Ausdauersportler/IMAC-EFI-BOOT-SCREEN/images/0201jumpers.jpg

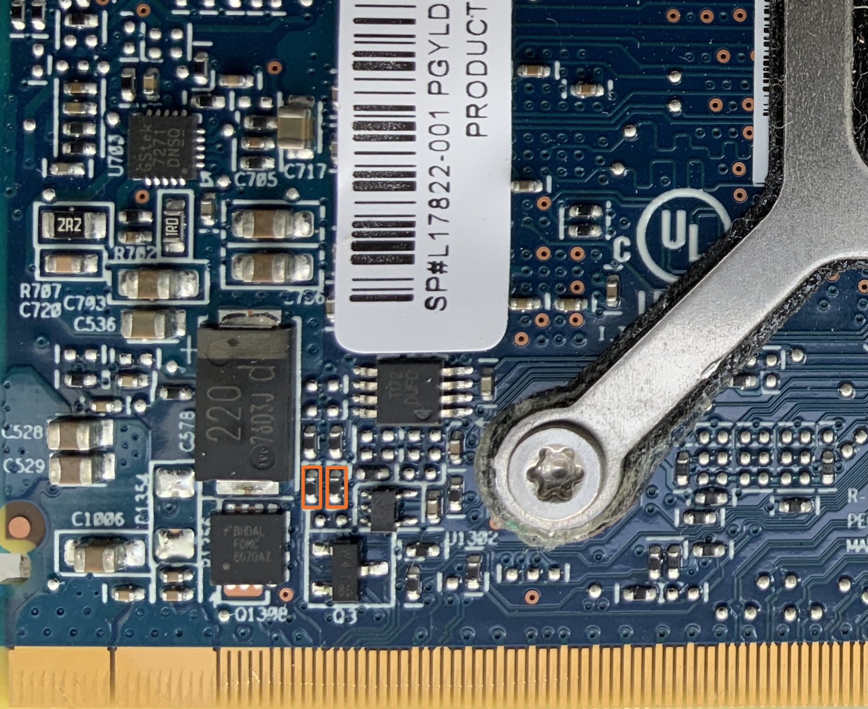
images/0201jumpers.jpg
