Ausdauersportler/IMAC-EFI-BOOT-SCREEN/images/0201jumpers_removed.jpg

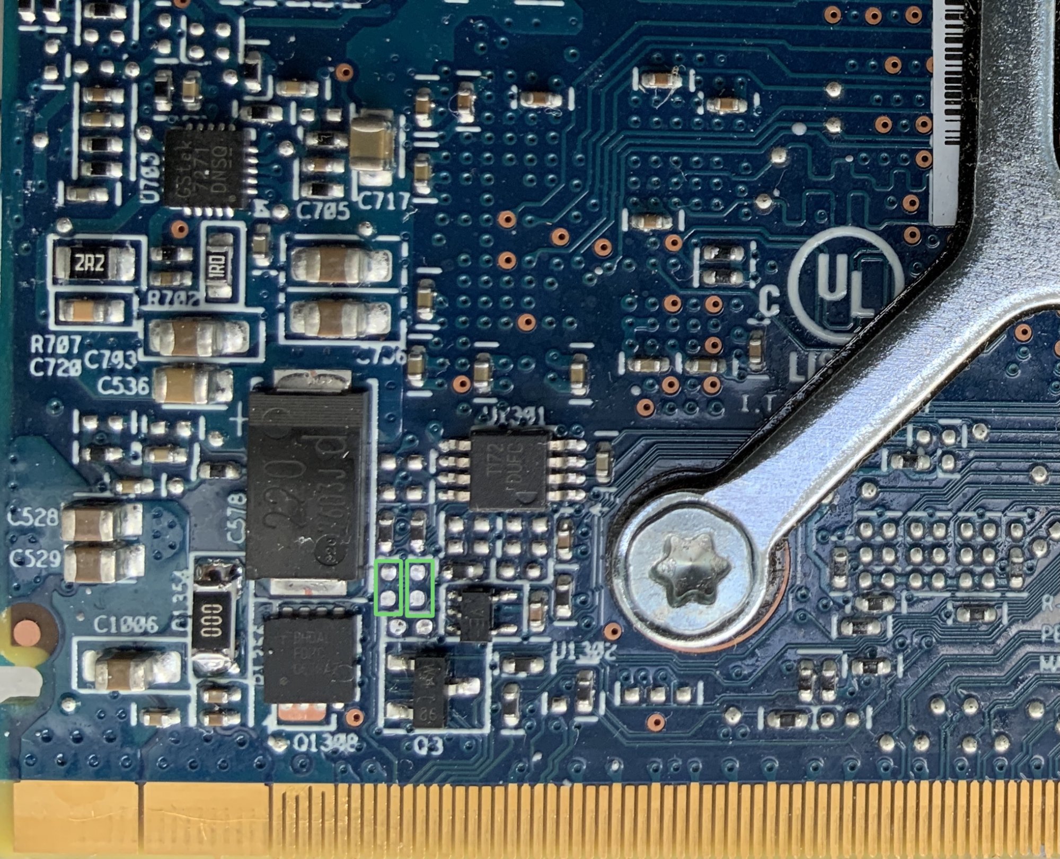
images/0201jumpers_removed.jpg
