Ausdauersportler/IMAC-EFI-BOOT-SCREEN/images/add-onPCB_conn.png

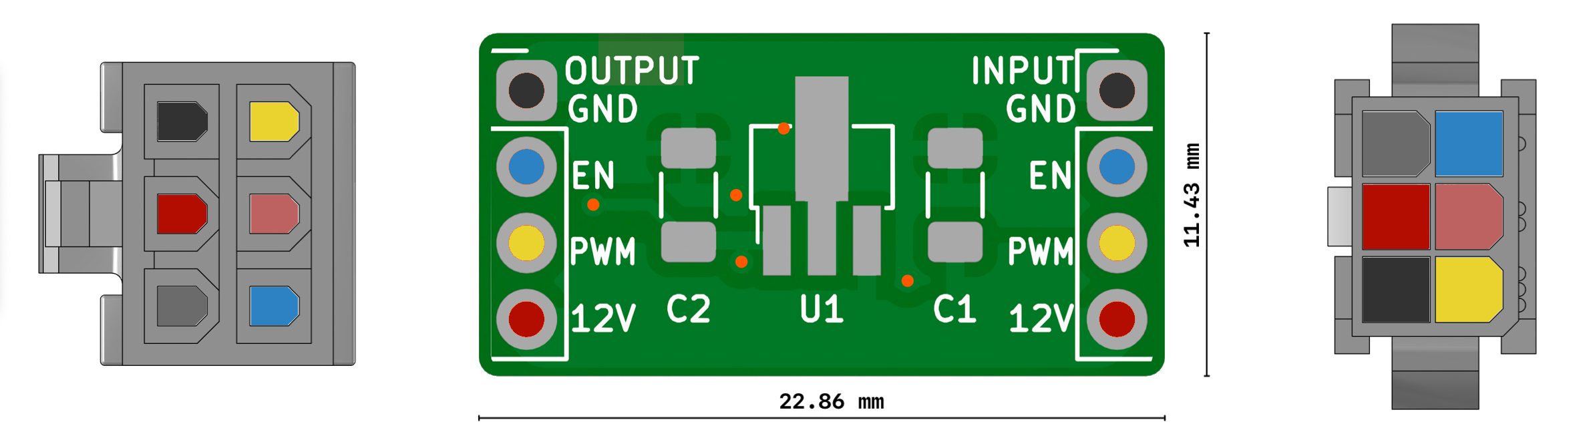
images/add-onPCB_conn.png
