Ausdauersportler/IMAC-EFI-BOOT-SCREEN/images/bottom_moddedWX4170.jpg

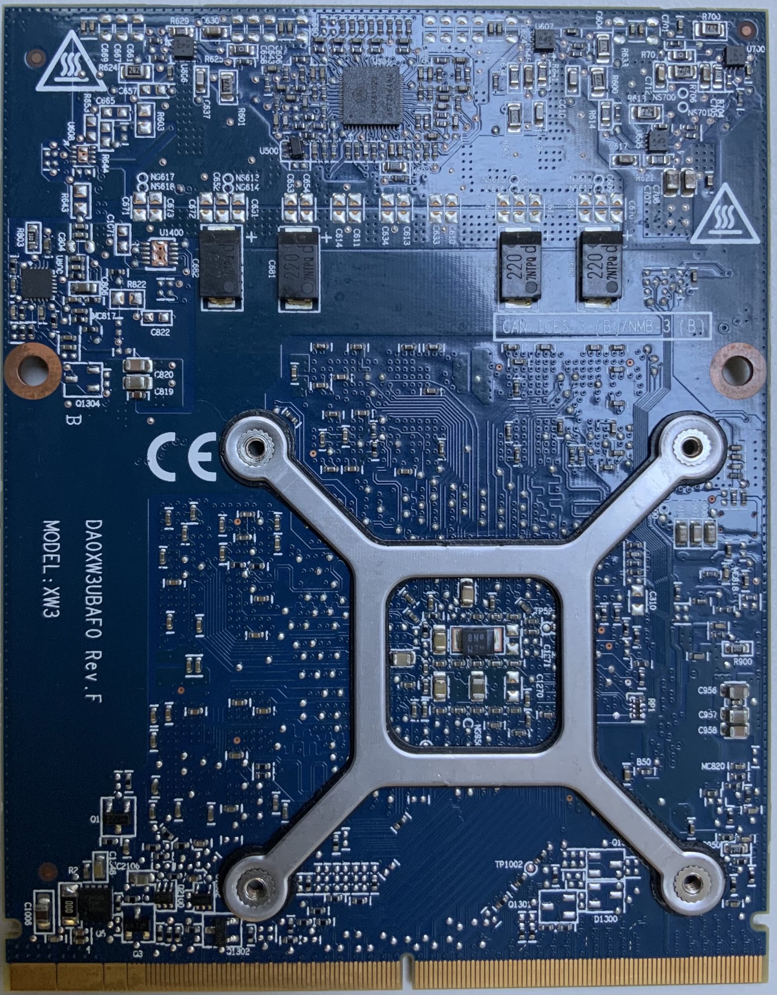
images/bottom_moddedWX4170.jpg
