Ausdauersportler/IMAC-EFI-BOOT-SCREEN/images/bottom_origWX4170.jpg

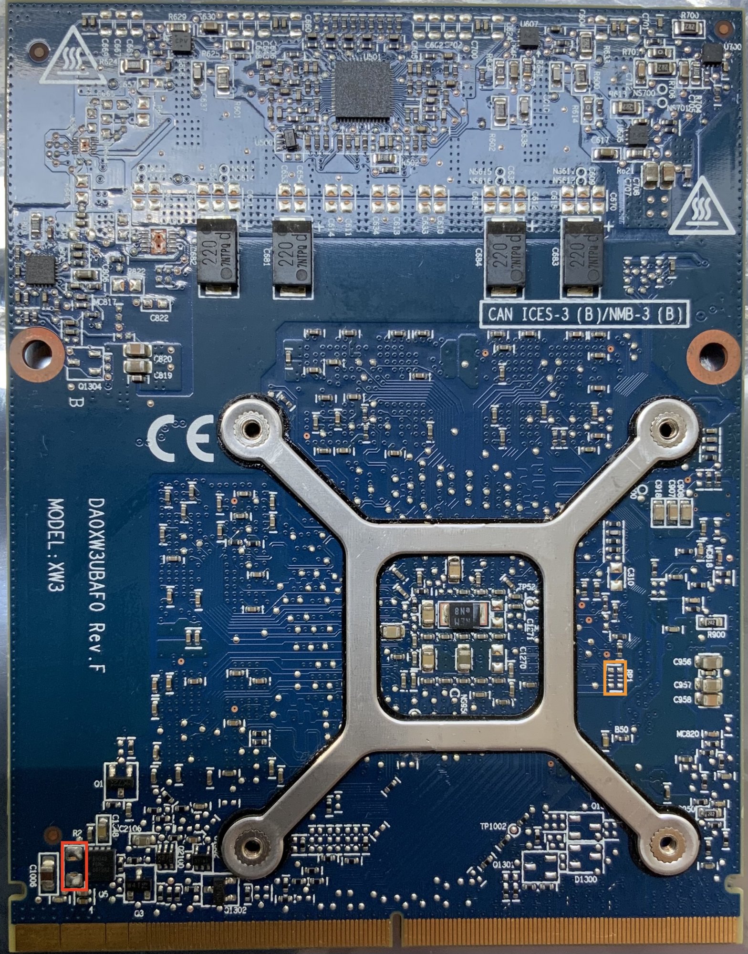
images/bottom_origWX4170.jpg
