Ausdauersportler/IMAC-EFI-BOOT-SCREEN/images/EFI-TABLES.png

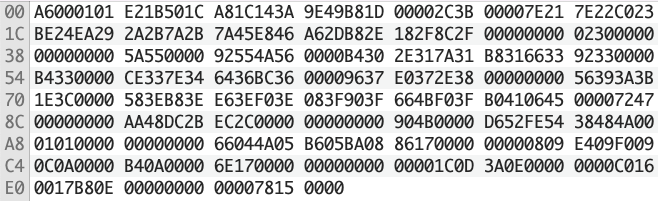
images/EFI-TABLES.png
