Ausdauersportler/IMAC-EFI-BOOT-SCREEN/images/GOP-TABLES.png

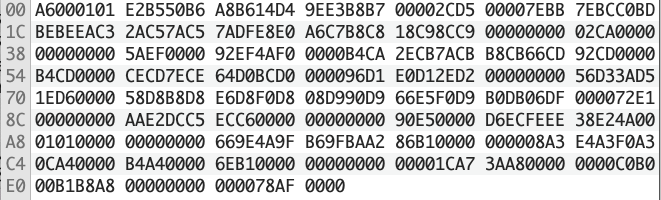
images/GOP-TABLES.png
