Ausdauersportler/IMAC-EFI-BOOT-SCREEN/images/GRML-FLASH.png

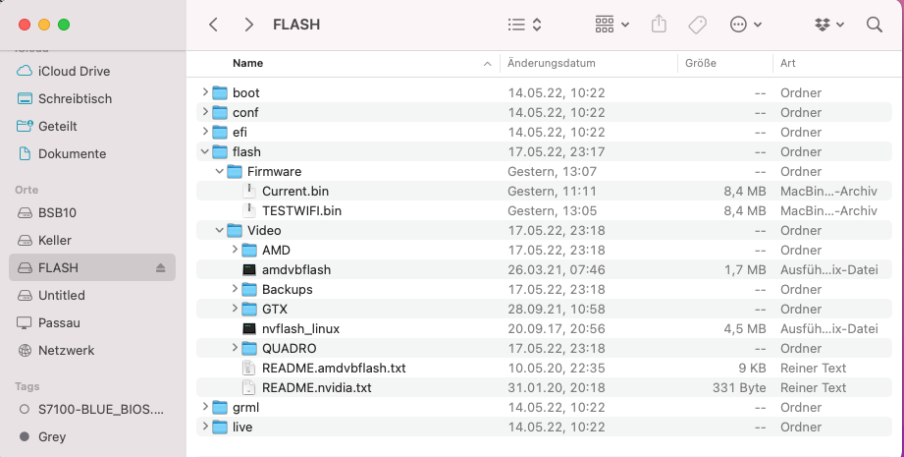
images/GRML-FLASH.png
