Ausdauersportler/IMAC-EFI-BOOT-SCREEN/images/hot-wire-pwm-EG.jpg

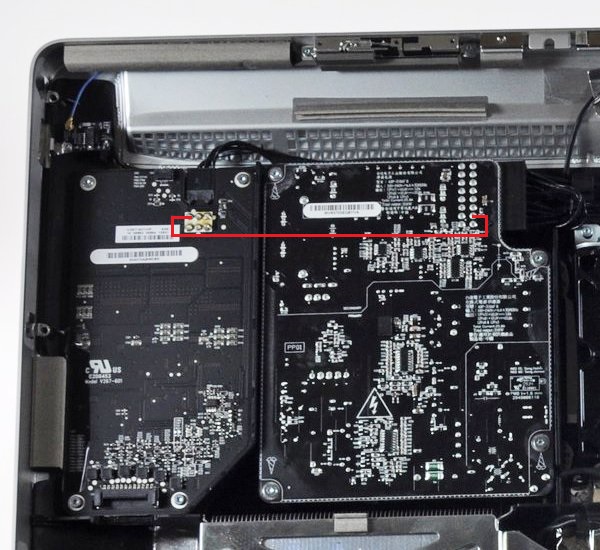
images/hot-wire-pwm-EG.jpg
