Ausdauersportler/IMAC-EFI-BOOT-SCREEN/images/M370-Tables.png

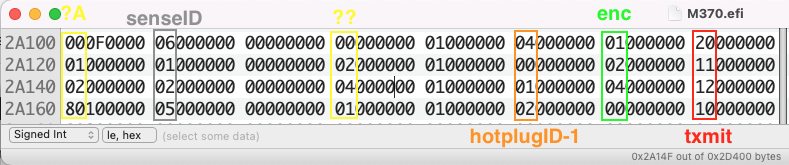
images/M370-Tables.png
