Ausdauersportler/IMAC-EFI-BOOT-SCREEN/images/modded.jpg

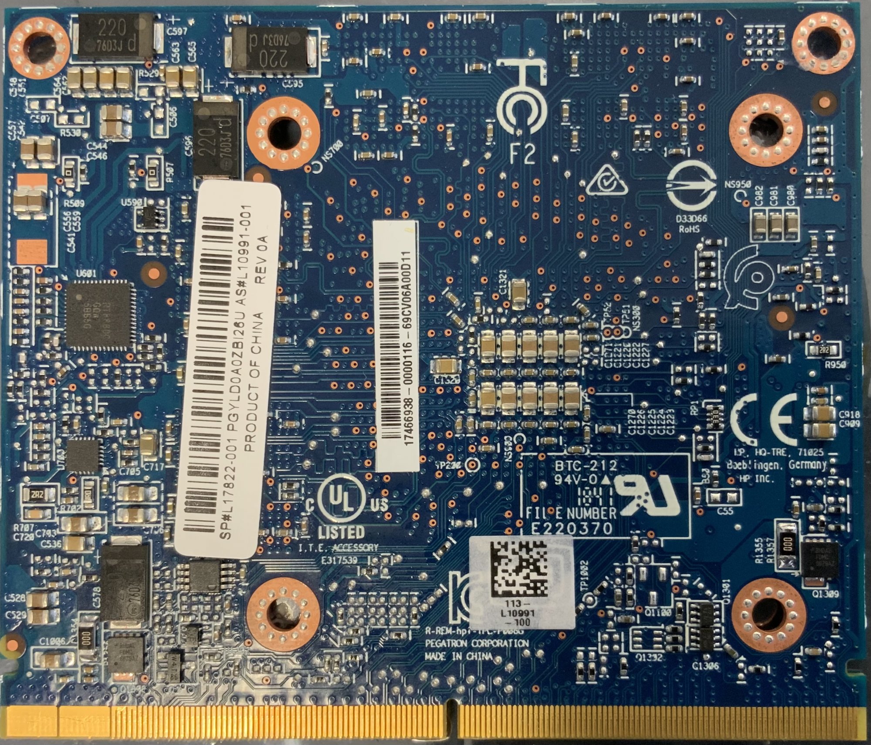
images/modded.jpg
