Ausdauersportler/IMAC-EFI-BOOT-SCREEN/images/RX5500XT_HeatSink_Mods.jpg

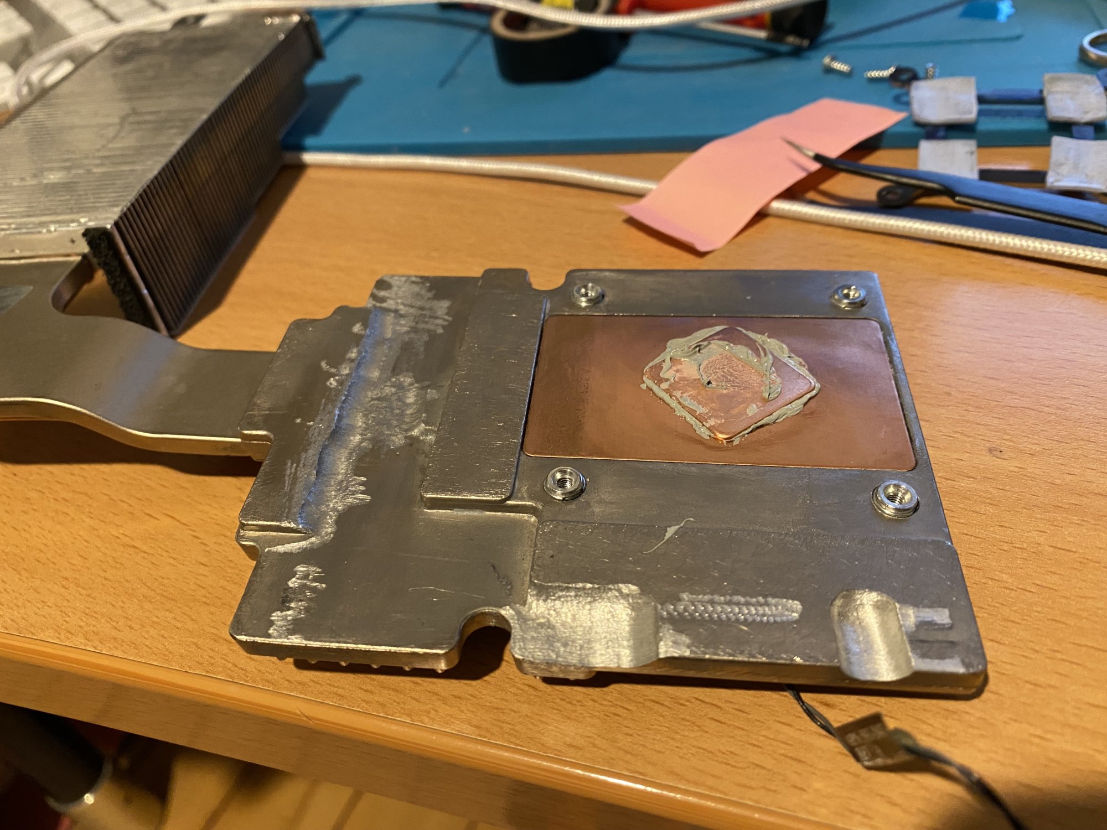
images/RX5500XT_HeatSink_Mods.jpg
