Ausdauersportler/IMAC-EFI-BOOT-SCREEN/images/sch_addonPCB.png

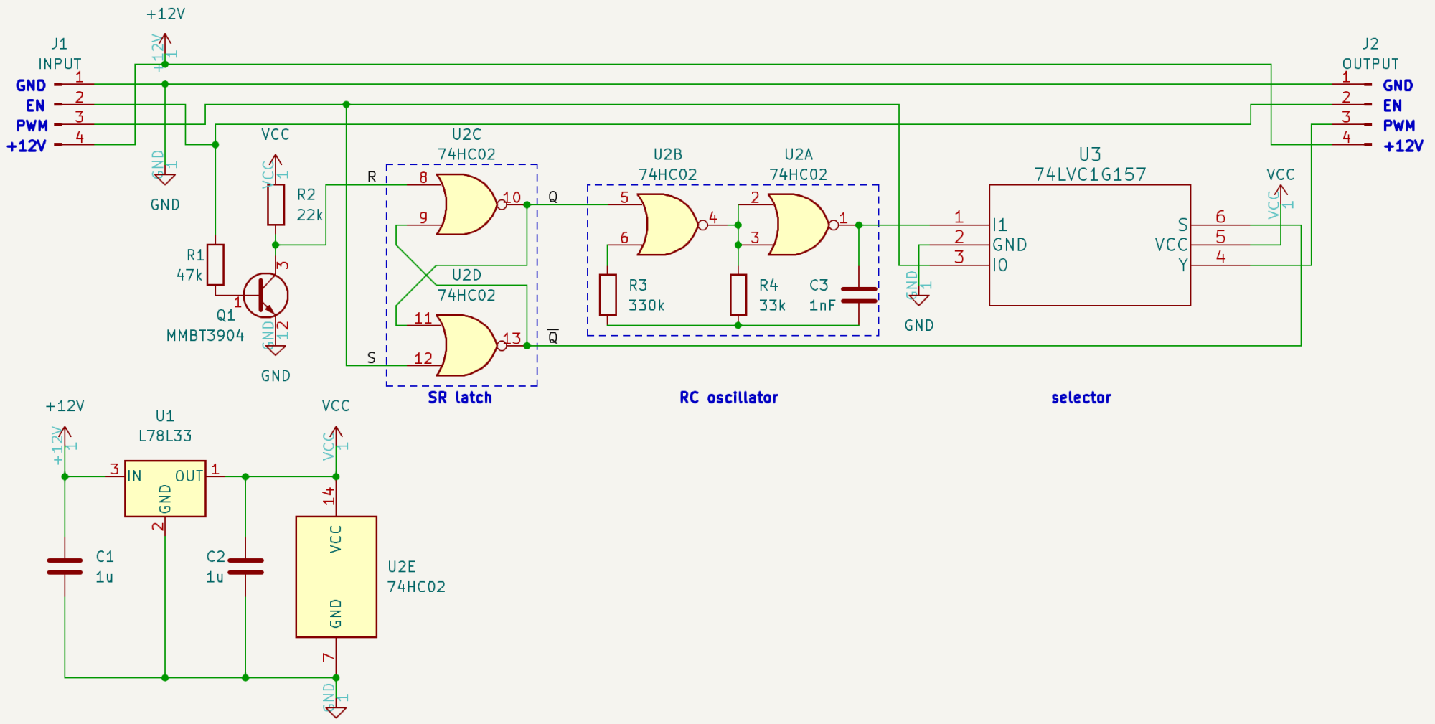
images/sch_addonPCB.png
