Ausdauersportler/IMAC-EFI-BOOT-SCREEN/images/top_moddedWX4170.jpg

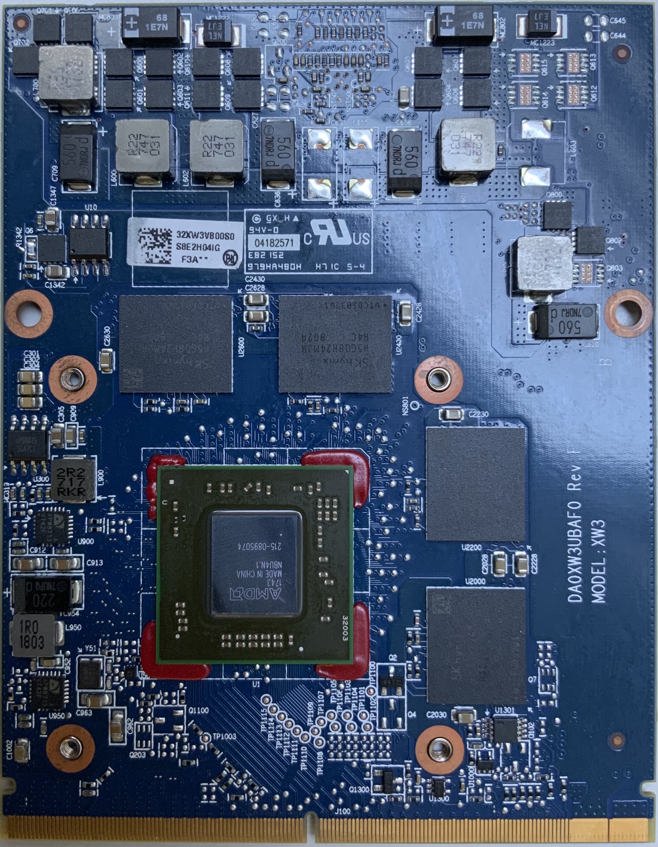
images/top_moddedWX4170.jpg
