Ausdauersportler/IMAC-EFI-BOOT-SCREEN/images/top_origWX4170.jpg

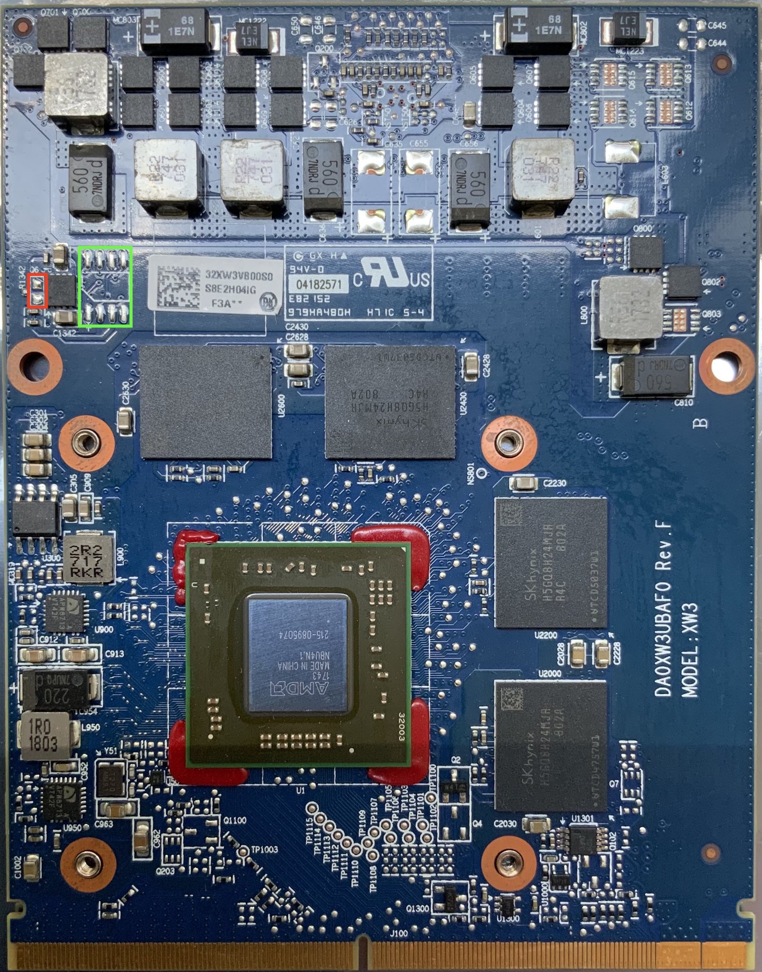
images/top_origWX4170.jpg
