Ausdauersportler/IMAC-EFI-BOOT-SCREEN/images/UEFITool-NE.png

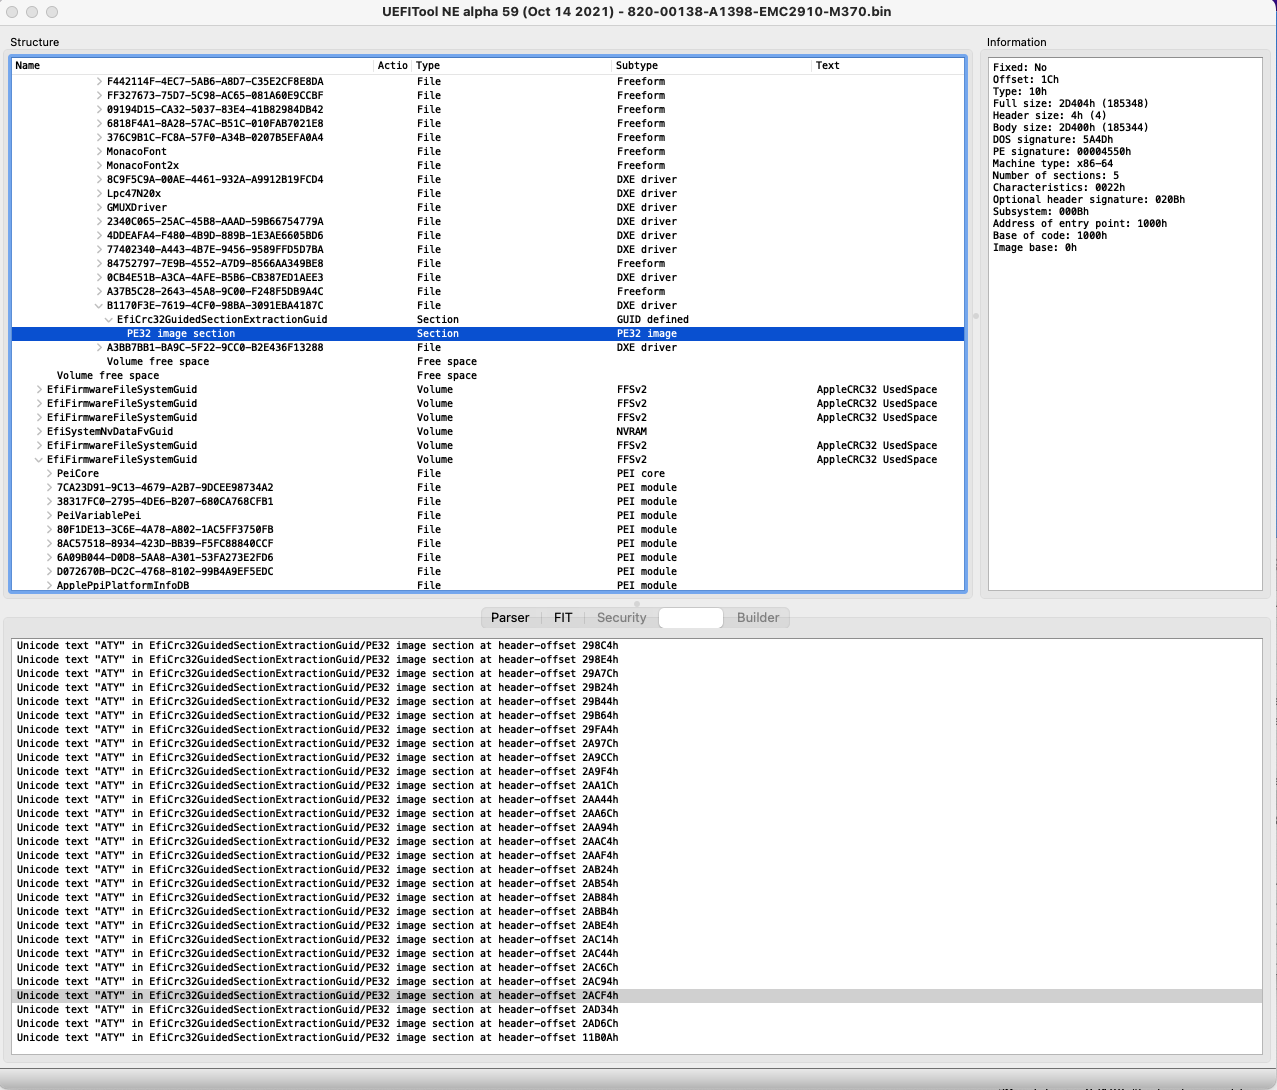
images/UEFITool-NE.png
