Ausdauersportler/IMAC-EFI-BOOT-SCREEN/images/unmodded.jpg

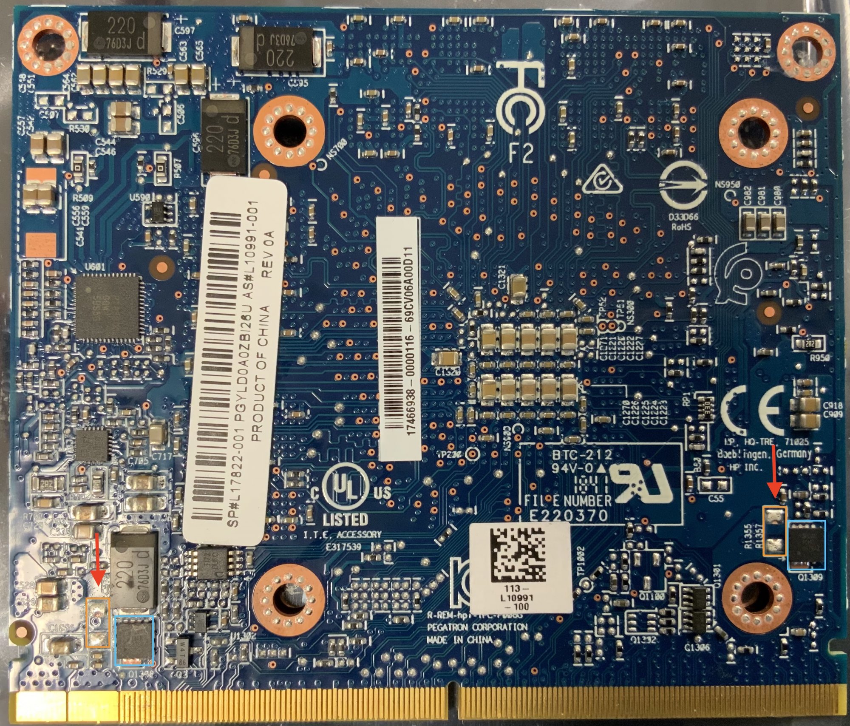
images/unmodded.jpg
