Ausdauersportler/IMAC-EFI-BOOT-SCREEN/images/W5170M-COMPARE_TABLES.png

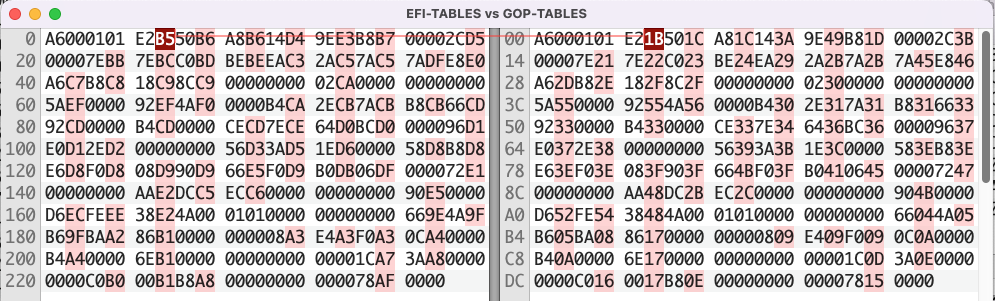
images/W5170M-COMPARE_TABLES.png
