Ausdauersportler/IMAC-EFI-BOOT-SCREEN/images/W5170M-EFI-HEADER.png

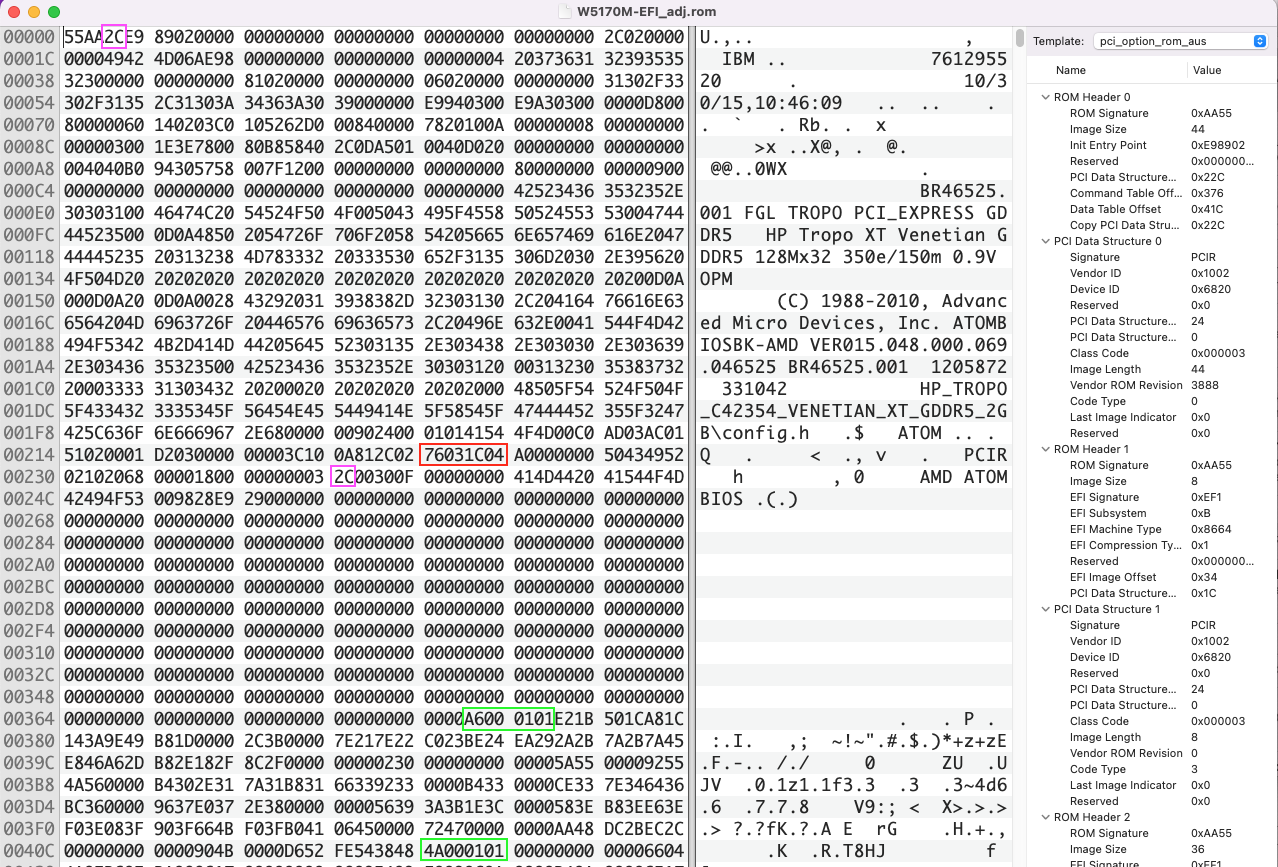
images/W5170M-EFI-HEADER.png
