Ausdauersportler/IMAC-EFI-BOOT-SCREEN/images/W5170M-GOP-HEADER.png

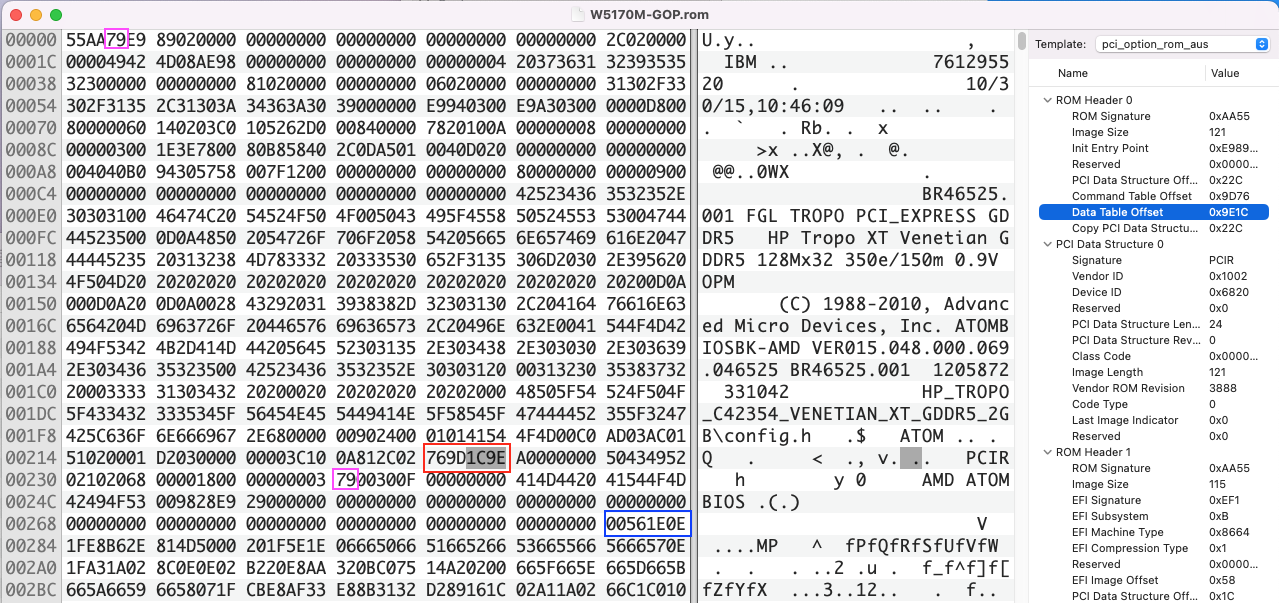
images/W5170M-GOP-HEADER.png
