Ausdauersportler/IMAC-EFI-BOOT-SCREEN/images/W5170M-SMBUS.png

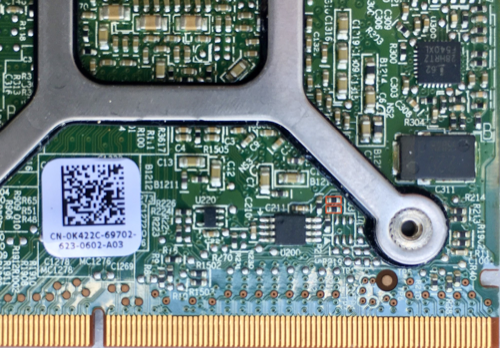
images/W5170M-SMBUS.png
