Ausdauersportler/IMAC-EFI-BOOT-SCREEN/images/WX4130-TEMPS.png

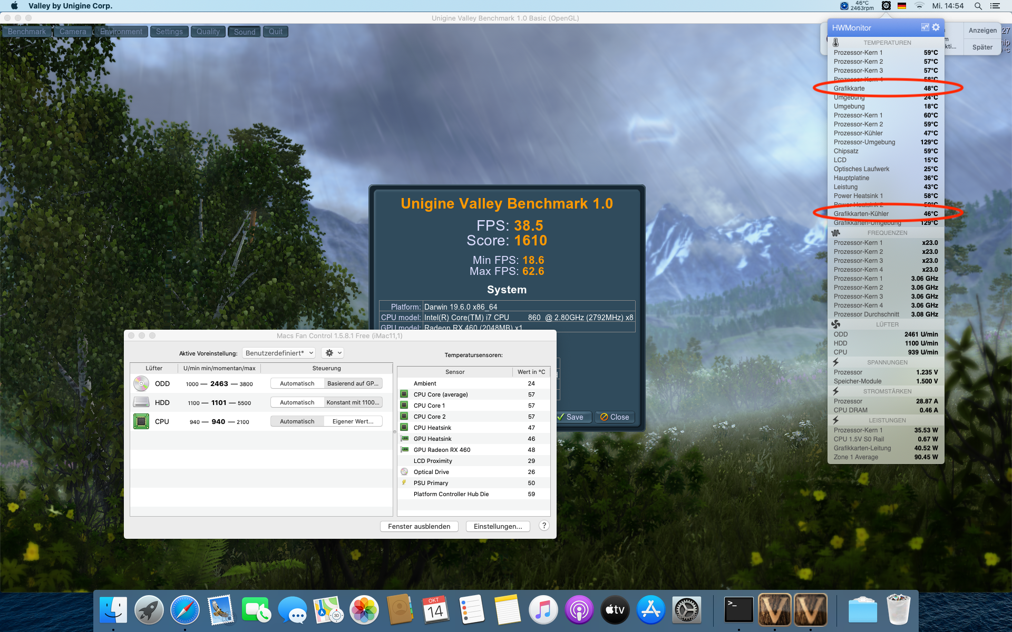
images/WX4130-TEMPS.png
