Ausdauersportler/IMAC-EFI-BOOT-SCREEN/images/WX4170-0201jumpers.jpg

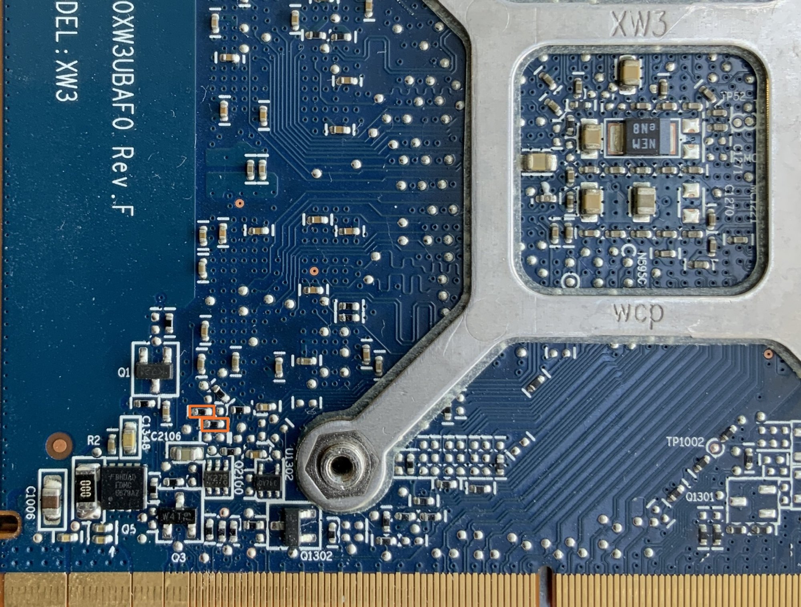
images/WX4170-0201jumpers.jpg
