Ausdauersportler/IMAC-EFI-BOOT-SCREEN/images/WX4170-0201jumpers_removed.jpg

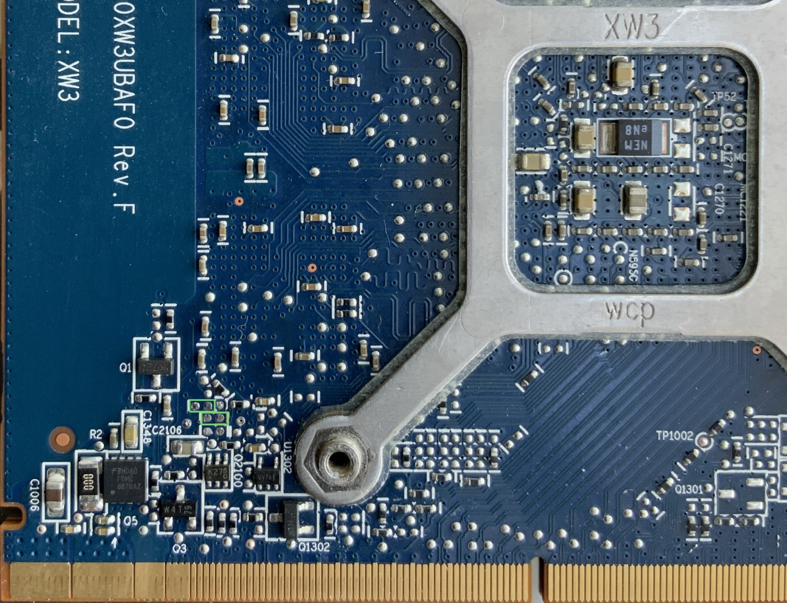
images/WX4170-0201jumpers_removed.jpg
