Ausdauersportler/IMAC-EFI-BOOT-SCREEN/images/WX4170AMD-noBIOS.png

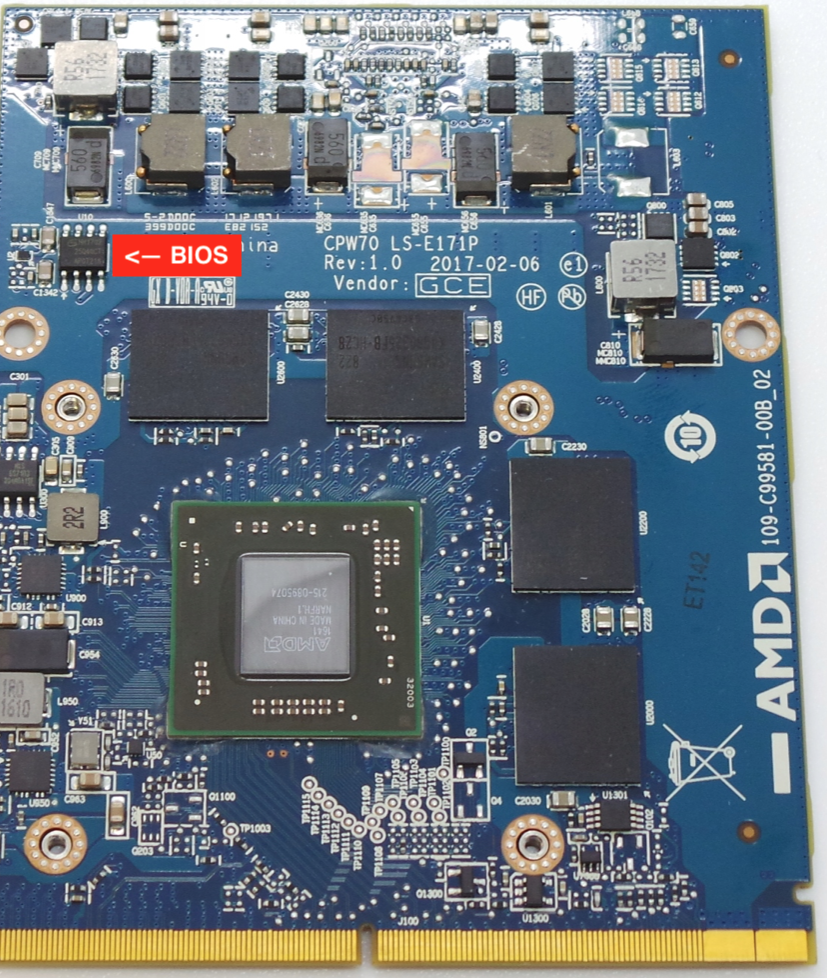
images/WX4170AMD-noBIOS.png
